okbrainhq/sMove/docs/revision-r2/final-export/connector-policy/README.md

# Current connector policy, historical stock receipts

JLC fits every SMT part: main 35, carrier 14, including J2/J4/J5. No manual-SMT assembly option. Source-yourself board connectors need a future THT redesign, not a drop-in substitution.

Adjacent JSON/HTML evidence is an unchanged historical retrieval snapshot. Its embedded retrieval dates remain authoritative; no stock recheck, allocation, price quote or sourcing action occurred during cleanup. See [connector guide](../../CONNECTORS.md).
