okbrainhq/sMove/docs/revision-r2/button-alignment/historical-active-snapshot/HISTORICAL.md

# Historical active snapshot

Byte-for-byte prose/reports from aligned predecessor b8f2836, before the screwless revision. NOT current build instructions. Old artifacts remain in Git history and the two-part-case reports. Current: docs/revision-r2/screwless and housing/README.md.
