okbrainhq/sMove/docs/revision-r2/final-export/STOCK.md

# R2 five-set stock / cost reconciliation

5 complete main+carrier sets; per-type spares=max(2,ceil(20% of five-set quantity)); archived public JLC evidence only, not live/reserved. C16780 capture lacks timestamp: age UNKNOWN; filesystem time not substituted. All stock needs recheck before ordering.

26 unique types, 49 fitted parts/set. Five-set parts: $144.8485; with planned spares: $201.5939; equivalent fitted parts/set: $28.9697. Not a quote; excludes all fabrication/assembly, shipping/tax and external kit items.

The ICM-20948 alone is $19.8222 at archived 1–9 tier; the earlier $12–15 complete-unit planning estimate (not a user-imposed budget) is not supported by this evidence. No alternative/design change is made.

Unknown/blocked selected electronic CIDs: none in archived counts; current availability remains unknown. C16780 snapshot age is UNKNOWN. External pack, cables and <=3.2mm-head nylon hardware availability remains UNKNOWN.

|CID|MPN|Per set|Five sets|Spares|Need|Archived stock|Unit USD|Captured UTC|
|---|---|---:|---:|---:|---:|---:|---:|---|
|C11702|0402WGF1001TCE|3|15|3|18|11201598|0.0039|2026-09-08T00:20:49.400154+00:00|
|C1525|CL05B104KO5NNNC|5|25|5|30|36581471|0.0046|2026-09-08T00:20:50.410107+00:00|
|C165948|TYPE-C-31-M-12|1|5|2|7|293622|0.1856|2026-09-08T00:20:45.317999+00:00|
|C16780|CL21A476MQYNNNE|2|10|2|12|2002508|0.1432|UNKNOWN|
|C176944|AP2112K-1.8TRG1|1|5|2|7|48017|0.1714|2026-09-08T00:20:44.382194+00:00|
|C19666|CL10A475KO8NNNC|3|15|3|18|3946402|0.0329|2026-09-08T00:20:51.295470+00:00|
|C25092|0402WGF220JTCE|2|10|2|12|7229717|0.0033|2026-09-08T00:20:49.034886+00:00|
|C25741|0402WGF1003TCE|3|15|3|18|12715118|0.0028|2026-09-08T00:20:47.815196+00:00|
|C25744|0402WGF1002TCE|5|25|5|30|30261401|0.0031|2026-09-08T00:20:47.532382+00:00|
|C25764|0402WGF2003TCE|1|5|2|7|1089048|0.0021|2026-09-08T00:25:11.014105+00:00|
|C25900|0402WGF4701TCE|5|25|5|30|19700436|0.0029|2026-09-08T00:20:48.227270+00:00|
|C25905|0402WGF5101TCE|2|10|2|12|8034614|0.0026|2026-09-08T00:20:48.742255+00:00|
|C25924|0402WGF8201TCE|1|5|2|7|259312|0.0021|2026-09-08T00:43:33.105544+00:00|
|C265102|S4B-PH-SM4-TB(LF)(SN)|2|10|2|12|35961|0.3064|2026-09-08T00:32:34.745109+00:00|
|C2838502|ESP32-C3-MINI-1-N4|1|5|2|7|17877|3.8336|2026-09-08T00:20:42.492803+00:00|
|C29277|CL21A226MPQNNNE|1|5|2|7|893220|0.151|2026-09-08T00:20:50.895627+00:00|
|C295747|S2B-PH-SM4-TB(LF)(SN)|1|5|2|7|29200|0.2396|2026-09-08T00:20:45.758974+00:00|
|C33196|PCA9306DCUR|1|5|2|7|3892|0.7164|2026-09-08T00:20:42.494117+00:00|
|C458749|LTST-C19HE1WT|1|5|2|7|129566|0.0727|2026-09-08T00:20:46.081432+00:00|
|C49338|PESD5V0S2BT,215|1|5|2|7|27792|0.092|2026-09-08T00:20:47.304475+00:00|
|C51118|AP2112K-3.3TRG1|1|5|2|7|64276|0.1709|2026-09-08T00:21:38.649761+00:00|
|C52923|CL05A105KA5NQNC|1|5|2|7|10442857|0.0121|2026-09-08T00:20:50.639102+00:00|
|C54313|BQ24074RGTR|1|5|2|7|915|2.1215|2026-09-08T00:43:33.105018+00:00|
|C720477|TS-1088-AR02016|2|10|2|12|816344|0.0556|2026-09-08T00:20:45.964228+00:00|
|C726001|ICM-20948|1|5|2|7|5031|19.8222|2026-09-08T00:20:42.493369+00:00|
|C7519|USBLC6-2SC6|1|5|2|7|44815|0.1825|2026-09-08T00:20:46.796515+00:00|
