okbrainhq/sMove/docs/revision-r2/button-labels/close-up.png

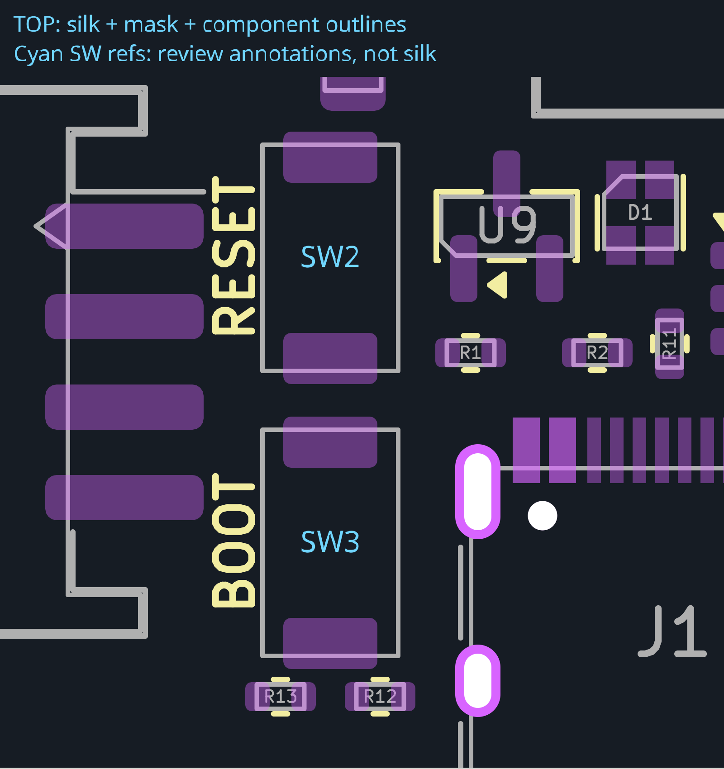
docs/revision-r2/button-labels/close-up.png
