okbrainhq/sMove/docs/revision-r2/compact-placement/images/A_32_two_M3.png

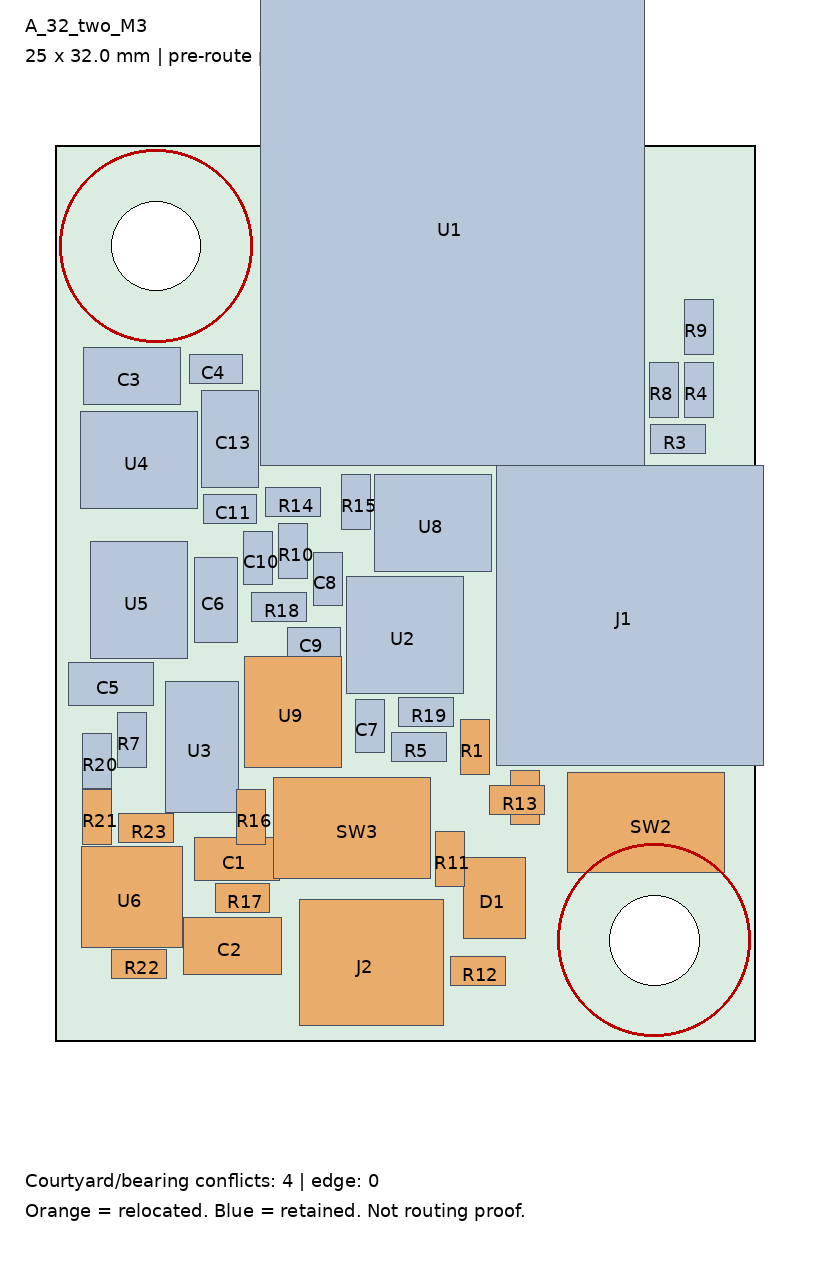
docs/revision-r2/compact-placement/images/A_32_two_M3.png
