okbrainhq/sMove/docs/revision-r2/compact-placement/images/before-pcb.png

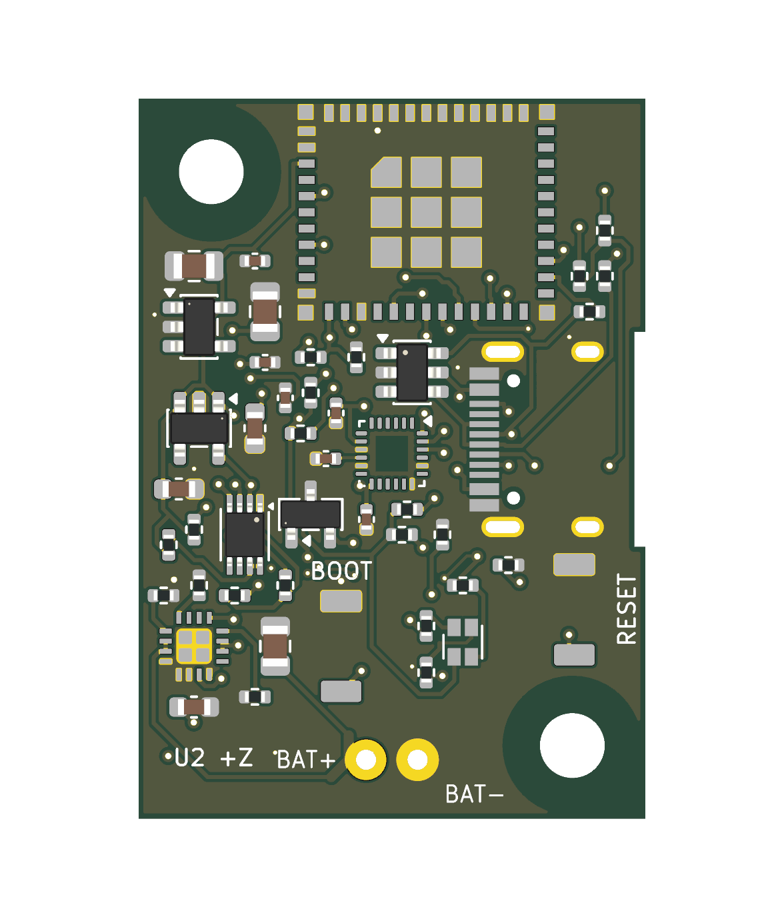
docs/revision-r2/compact-placement/images/before-pcb.png
