okbrainhq/sMove/docs/revision-r2/compact-placement/images/C_29_single_M3_tight.png

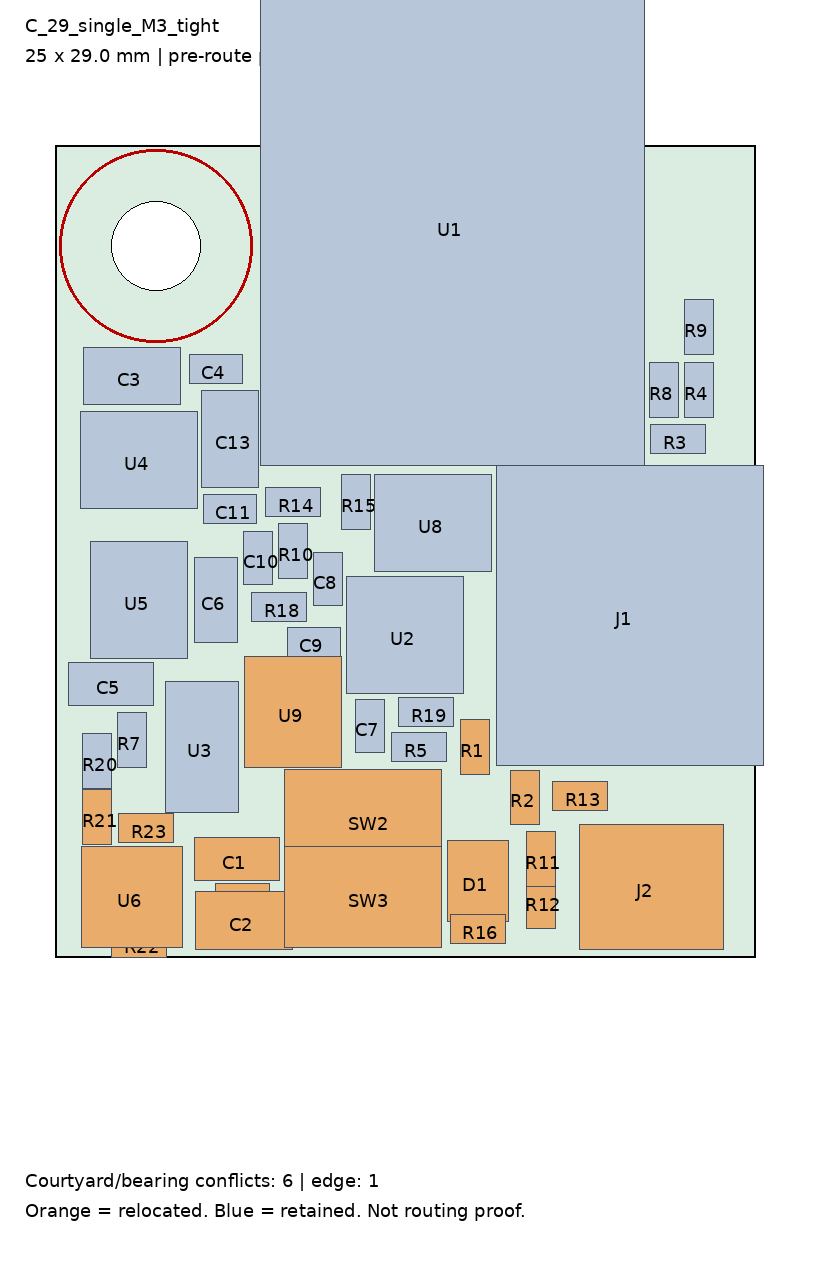
docs/revision-r2/compact-placement/images/C_29_single_M3_tight.png
