okbrainhq/sMove/docs/revision-r2/compact-placement/images/housing-comparison.png

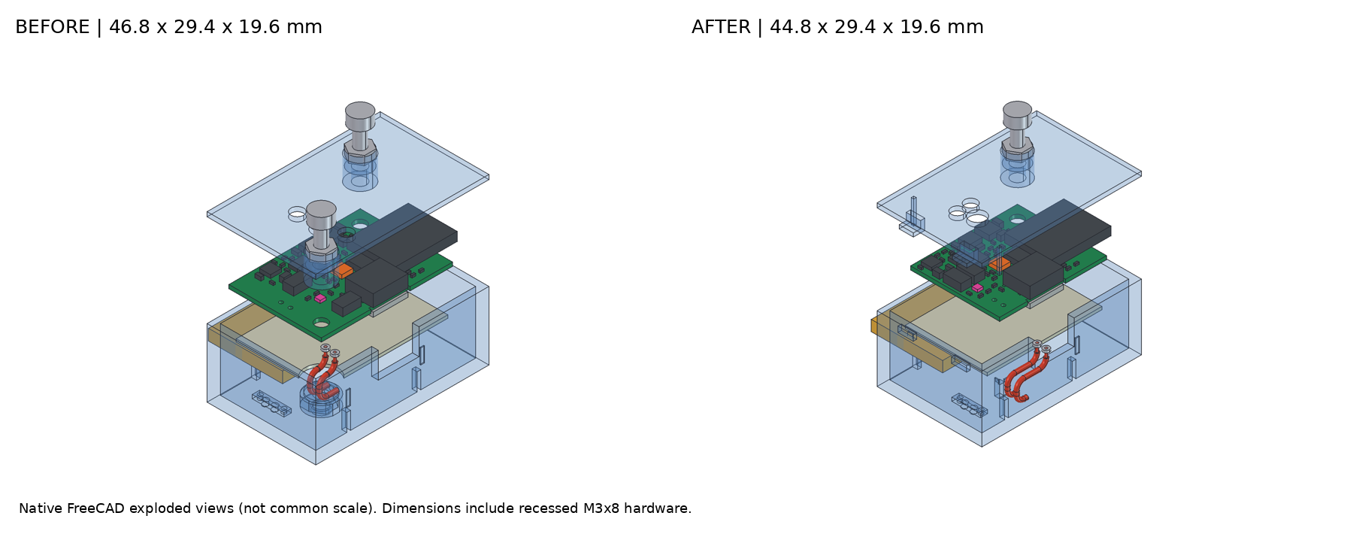
docs/revision-r2/compact-placement/images/housing-comparison.png
