okbrainhq/sMove/docs/revision-r2/compact-placement/images/pcb-comparison.png

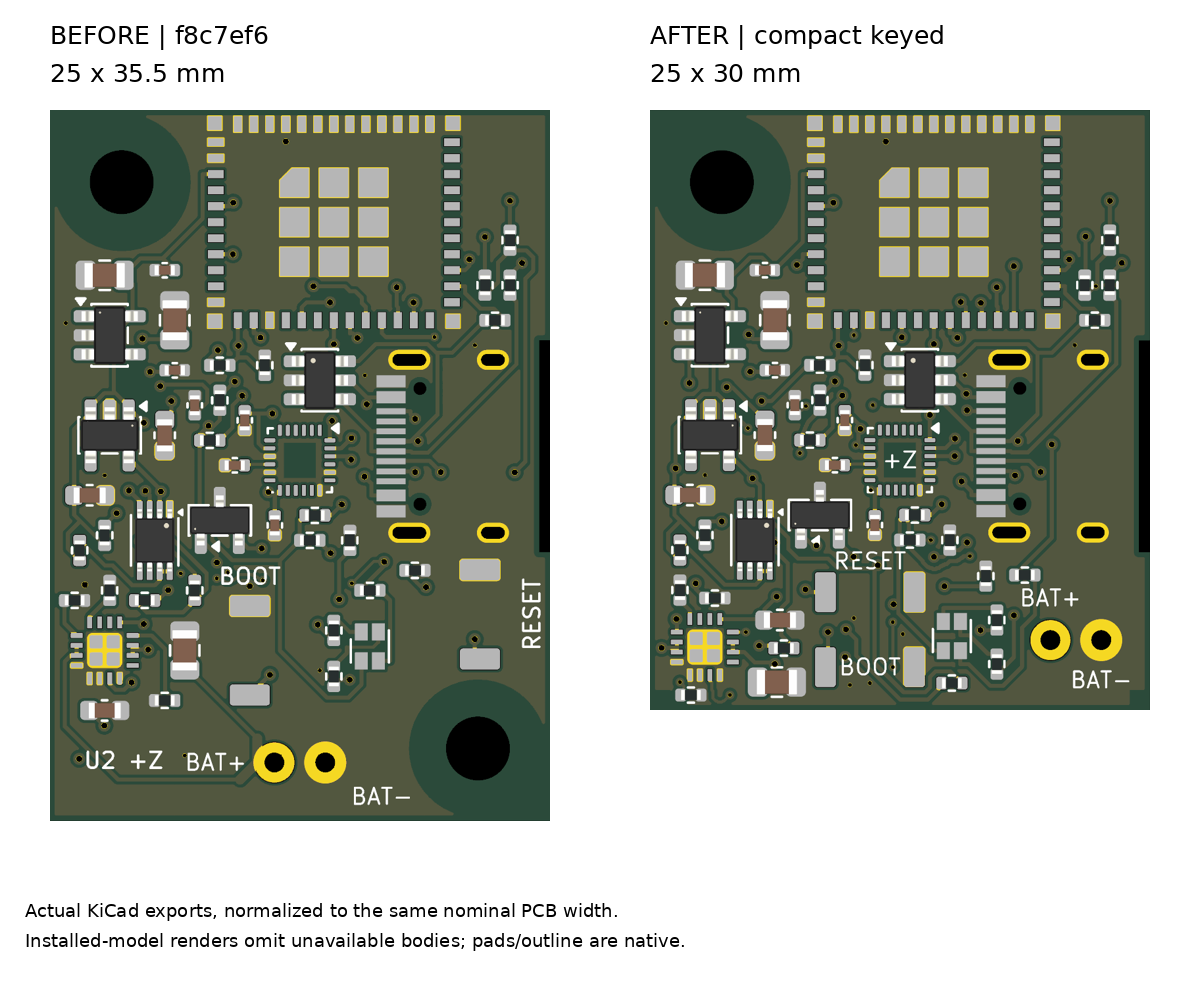
docs/revision-r2/compact-placement/images/pcb-comparison.png
