okbrainhq/sMove/docs/revision-r2/compact-placement/images/switch-drawing.png

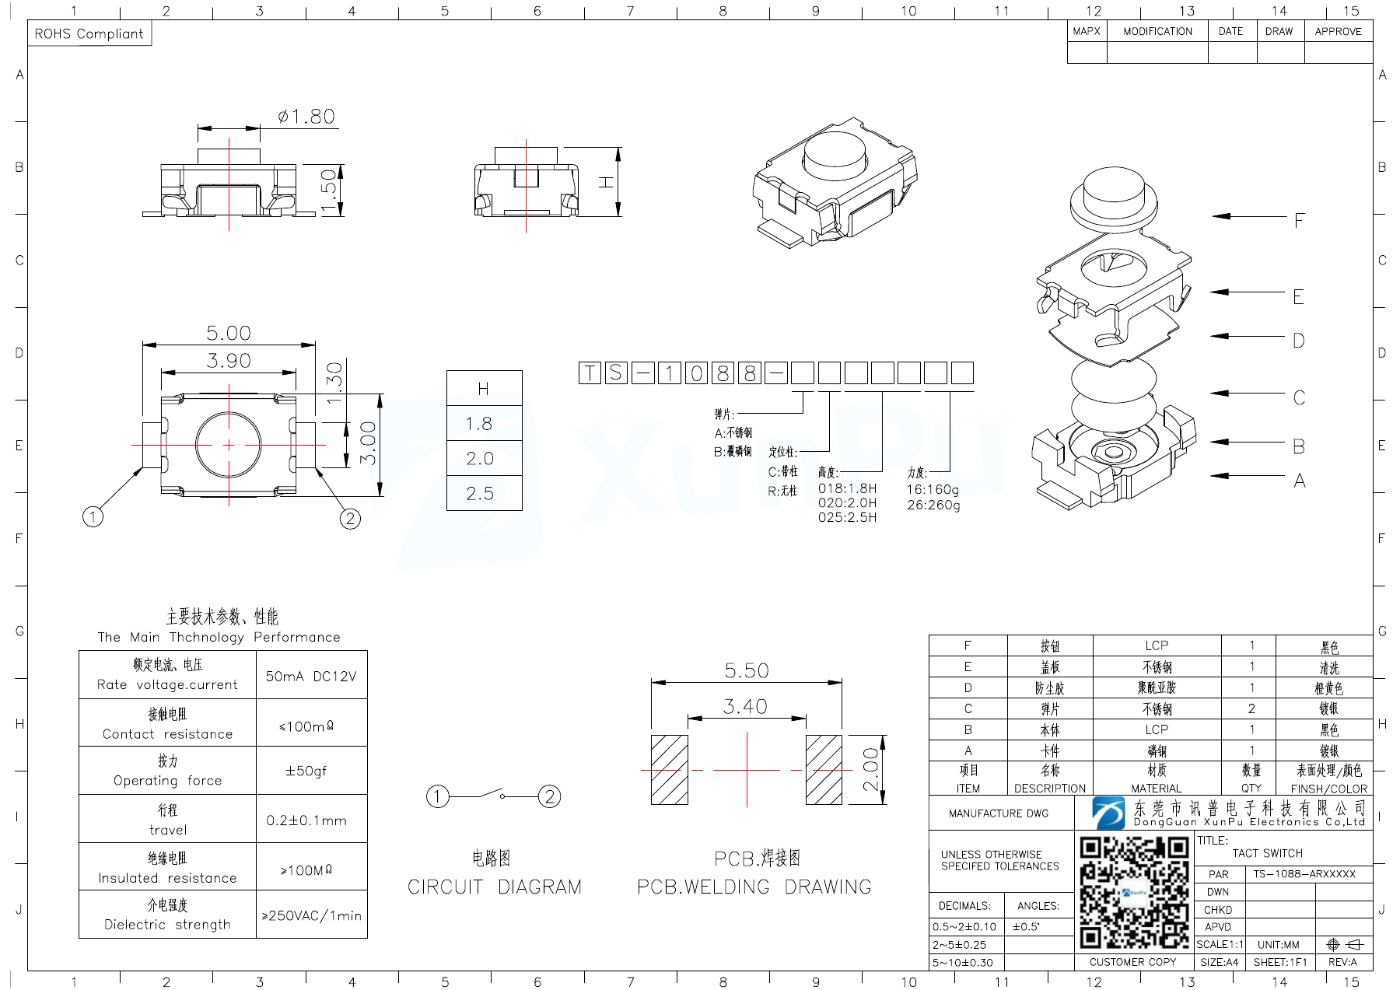
docs/revision-r2/compact-placement/images/switch-drawing.png
