okbrainhq/sMove/docs/revision-r2/main-routing/B.Cu.png

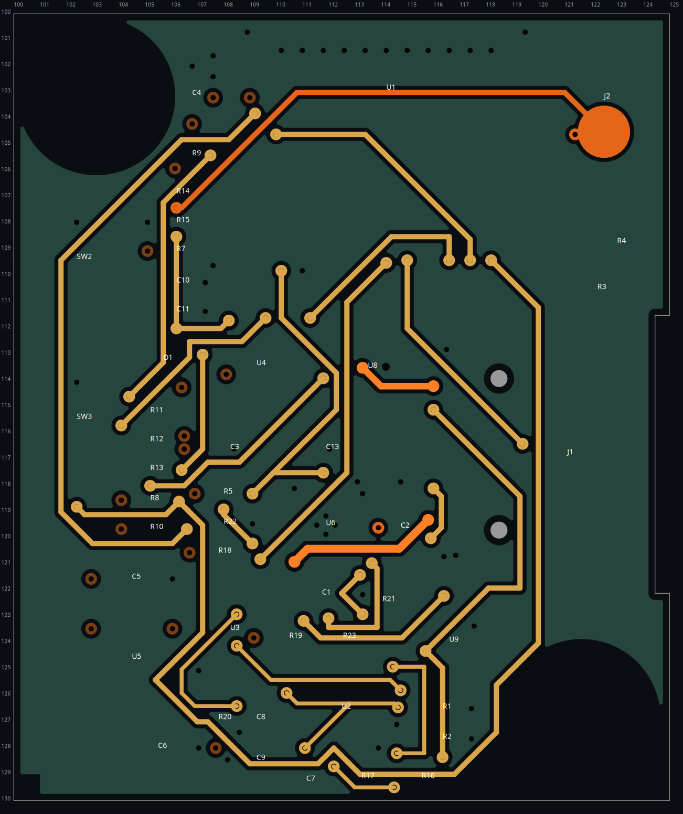
docs/revision-r2/main-routing/B.Cu.png
