okbrainhq/sMove/docs/revision-r2/main-routing/F.Cu.png

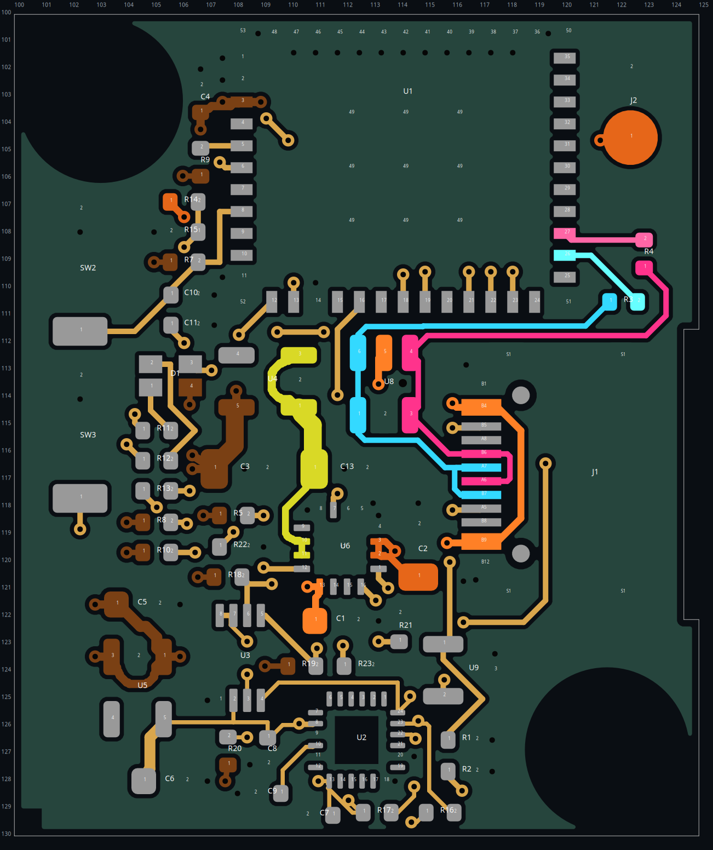
docs/revision-r2/main-routing/F.Cu.png
