okbrainhq/sMove/docs/revision-r2/placement-routing/before.png

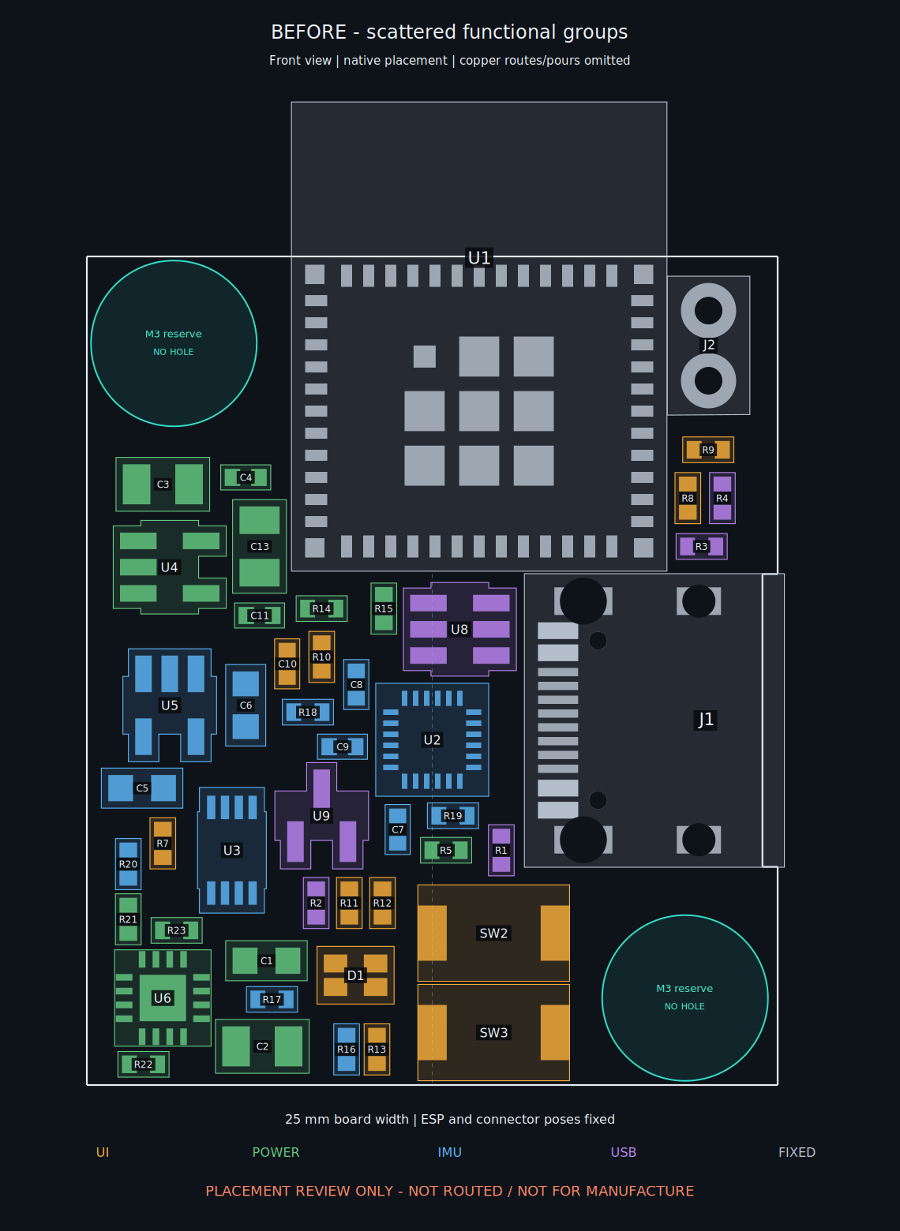
docs/revision-r2/placement-routing/before.png
