okbrainhq/sMove/docs/revision-r2/rgb-body/evidence/icm-axes.png

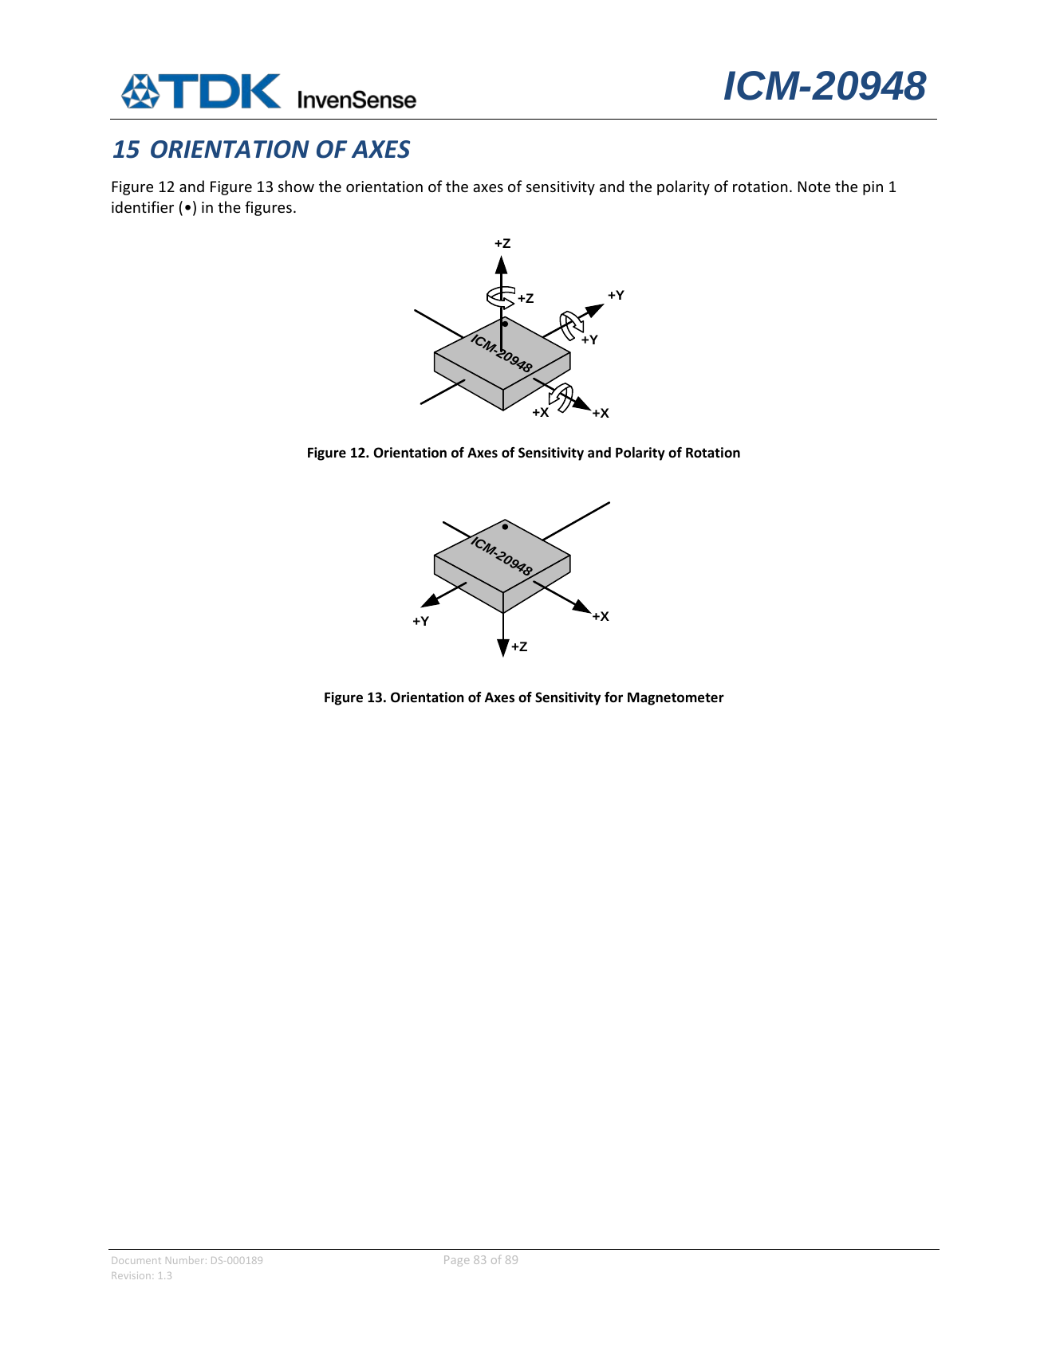
docs/revision-r2/rgb-body/evidence/icm-axes.png
