okbrainhq/sMove/docs/revision-r2/rgb-body/views/rgb-close-up.png

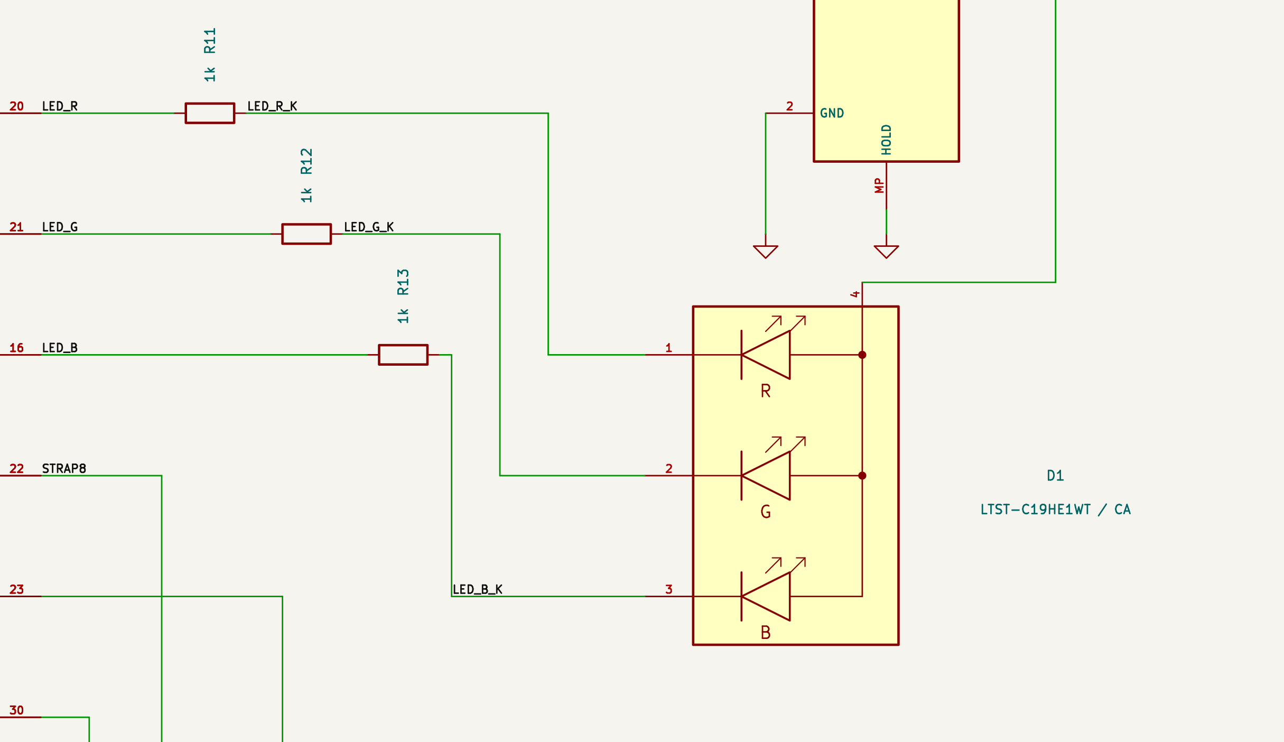
docs/revision-r2/rgb-body/views/rgb-close-up.png
