okbrainhq/sMove/docs/u4-thermal-eco/after-back.png

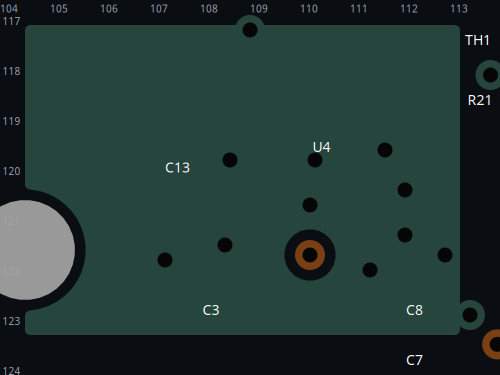
docs/u4-thermal-eco/after-back.png
