okbrainhq/sMove/housing/dist/midframe-bottom.png

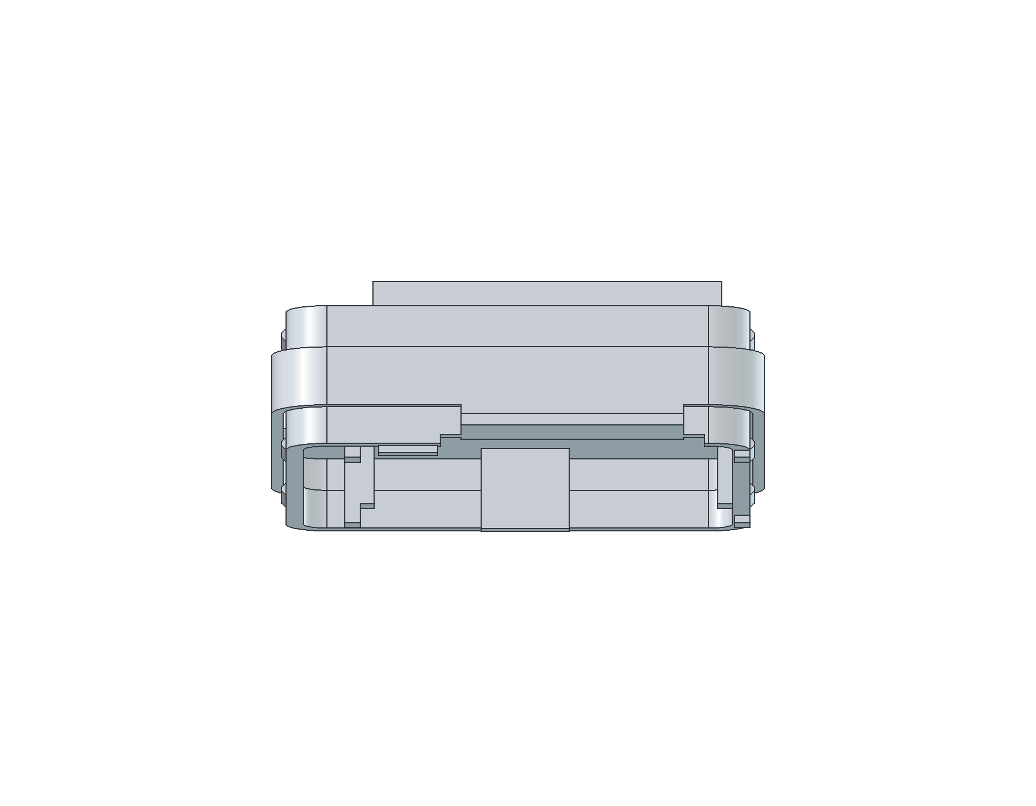
housing/dist/midframe-bottom.png
