okbrainhq/sMove/housing/dist/midframe-top.png

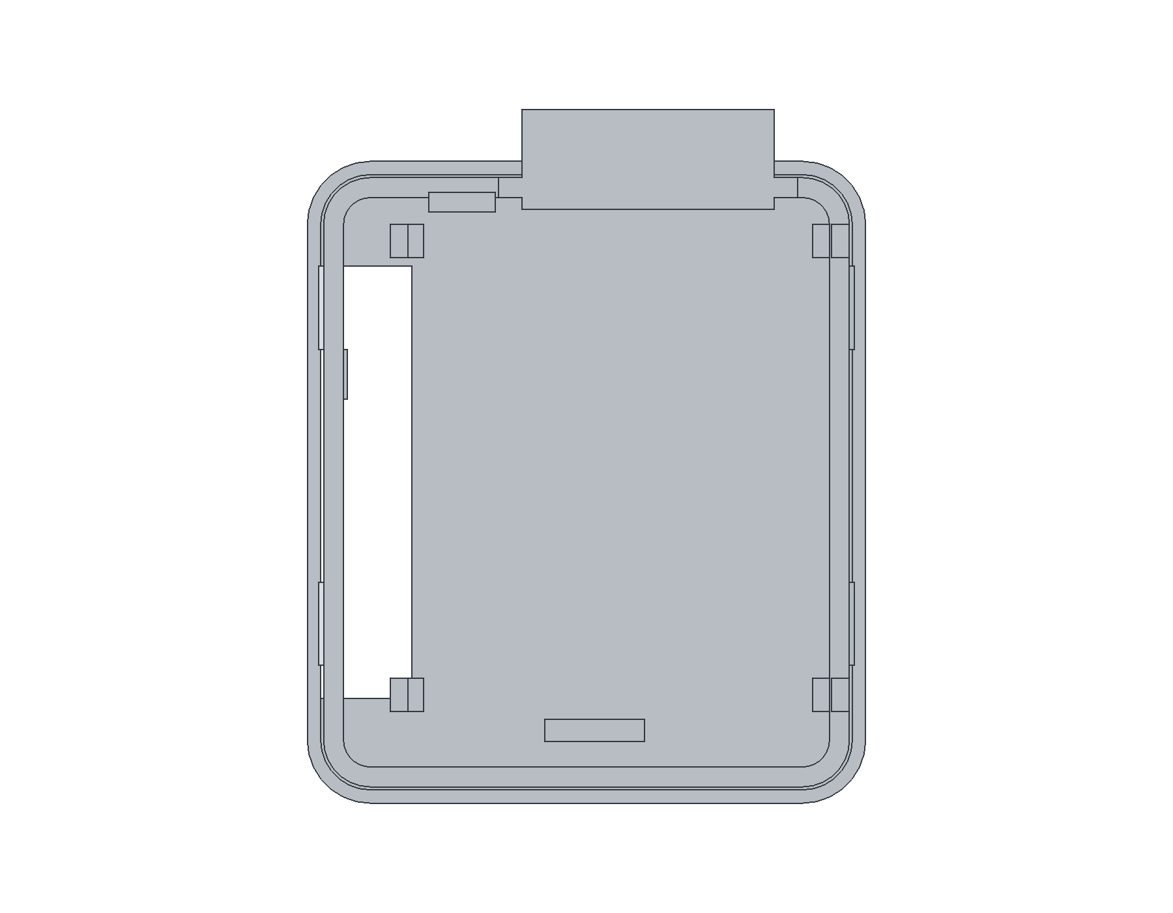
housing/dist/midframe-top.png
