okbrainhq/sMove/housing/dist/assembled-wire-path.png

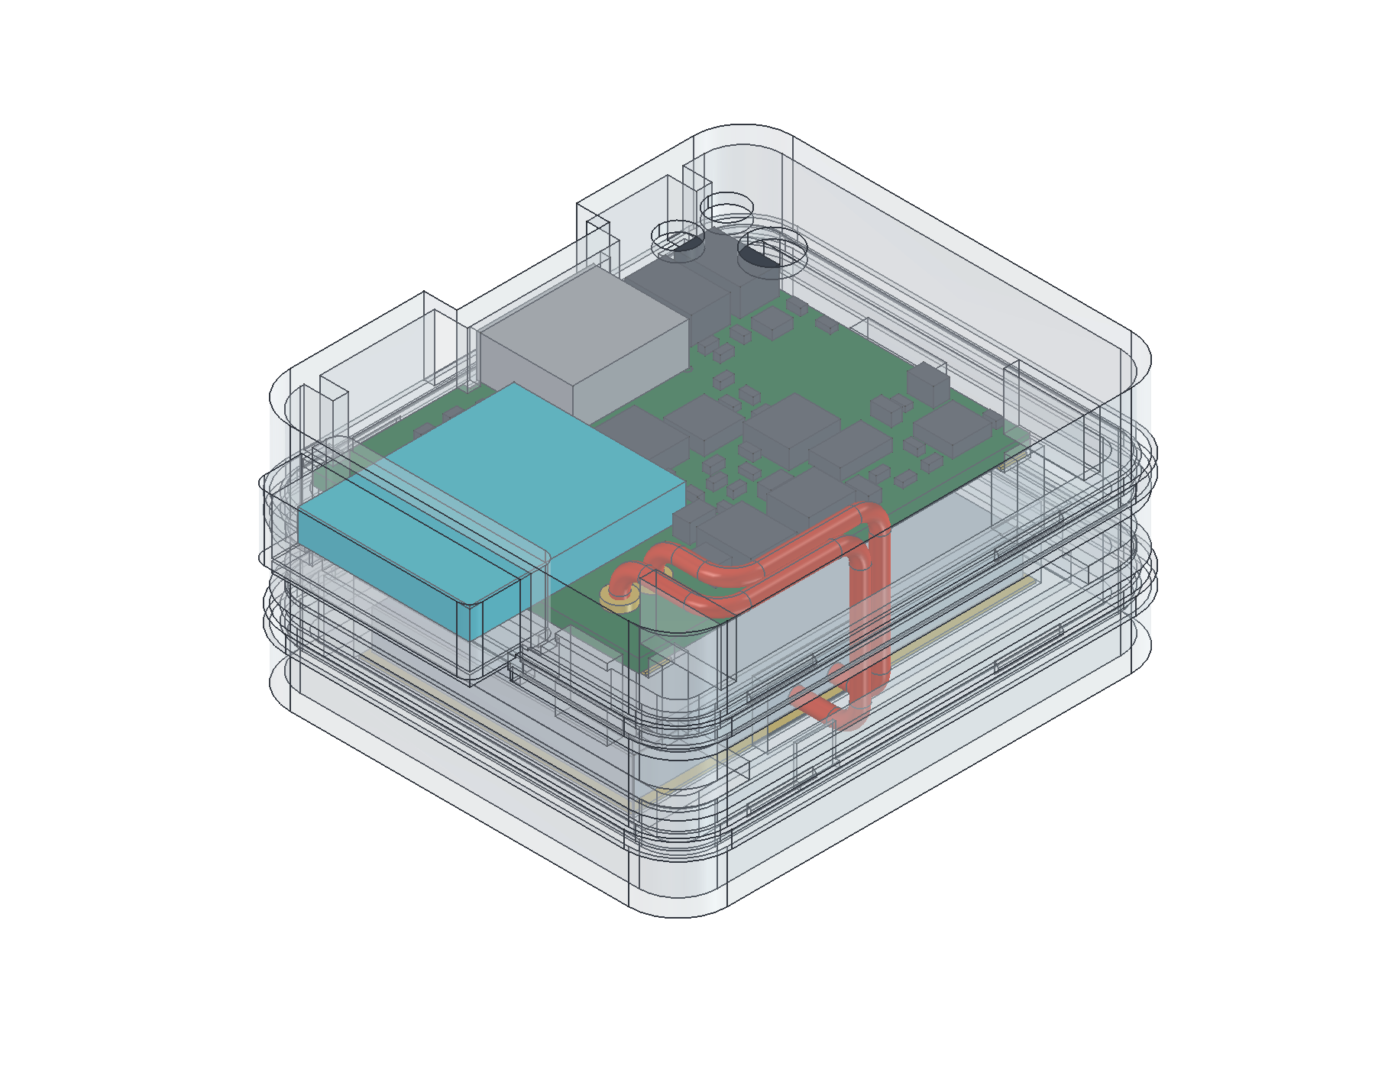
housing/dist/assembled-wire-path.png
