okbrainhq/sMove/housing/dist/assembled.png

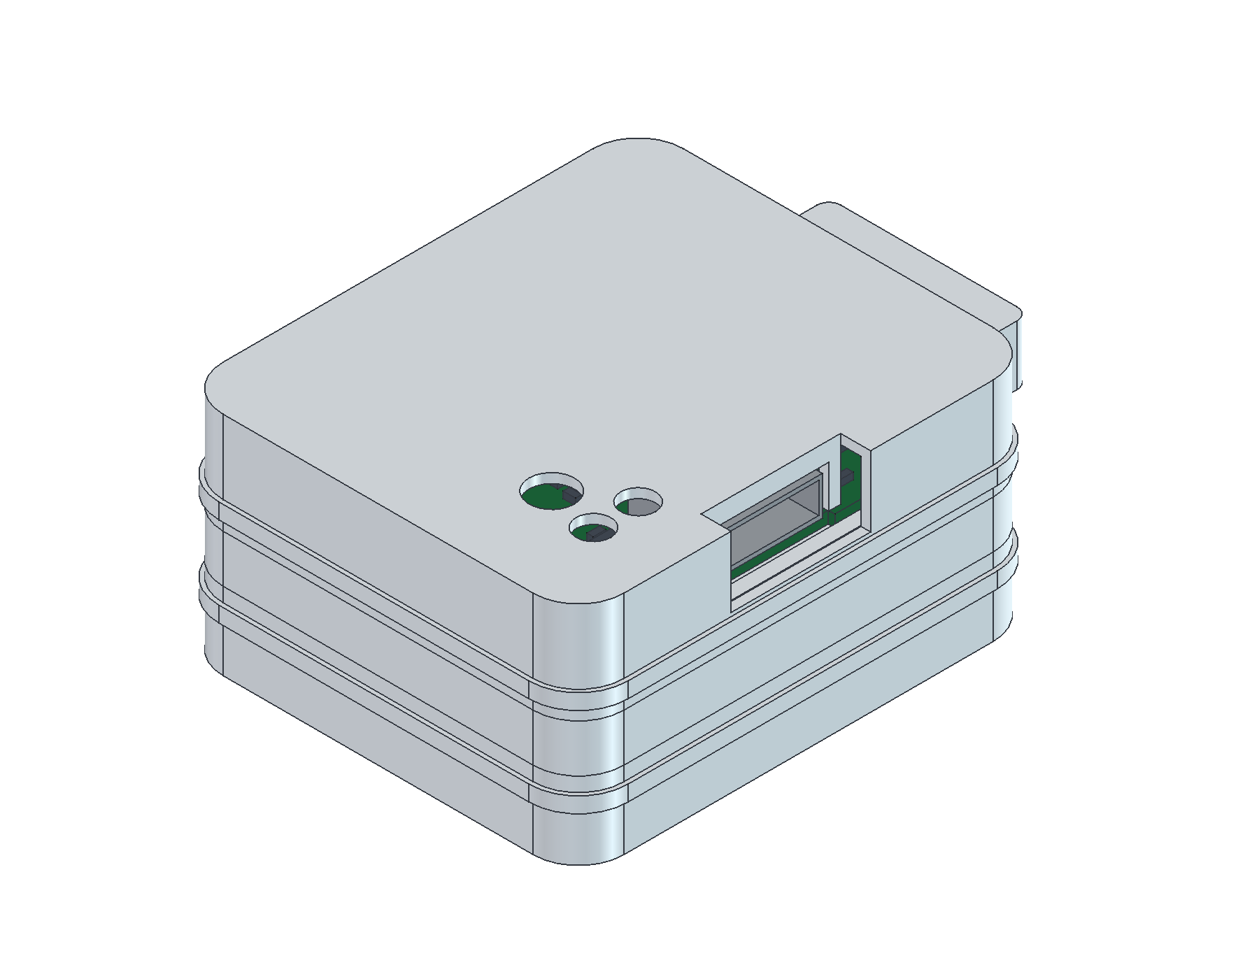
housing/dist/assembled.png
